jbilander/A500_Edge_Expansion_adapter/KiCad/A500_86pin_internal_adapter.sch

## KiCad design KiCad/A500_86pin_internal_adapter.sch (2021-07-18)

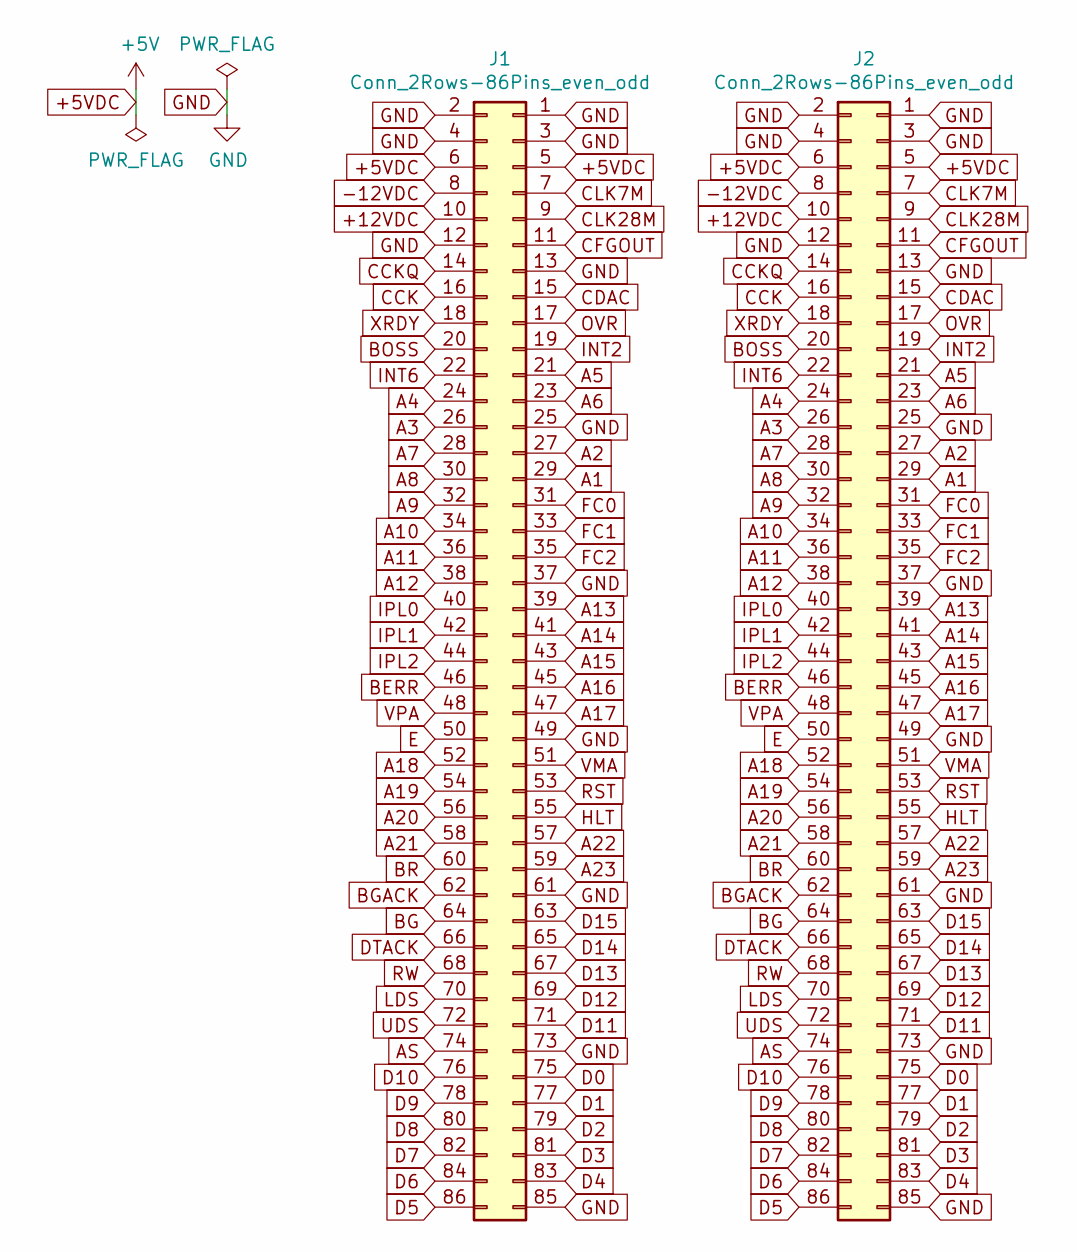
[picture p12: schematic A500_86pin_internal_adapter.sch]

Parts:
J1, J2: Conn_2Rows-86Pins_even_odd; DIP-86_even_odd_W5.08mm

Connections:
+5V: J1.5, J1.6, J2.5, J2.6
+12VDC: J1.10, J2.10
-12VDC: J1.8, J2.8
A1: J1.29, J2.29
A2: J1.27, J2.27
A3: J1.26, J2.26
A4: J1.24, J2.24
A5: J1.21, J2.21
A6: J1.23, J2.23
A7: J1.28, J2.28
A8: J1.30, J2.30
A9: J1.32, J2.32
A10: J1.34, J2.34
A11: J1.36, J2.36
A12: J1.38, J2.38
A13: J1.39, J2.39
A14: J1.41, J2.41
A15: J1.43, J2.43
A16: J1.45, J2.45
A17: J1.47, J2.47
A18: J1.52, J2.52
A19: J1.54, J2.54
A20: J1.56, J2.56
A21: J1.58, J2.58
A22: J1.57, J2.57
A23: J1.59, J2.59
AS: J1.74, J2.74
BERR: J1.46, J2.46
BG: J1.64, J2.64
BGACK: J1.62, J2.62
BOSS: J1.20, J2.20
BR: J1.60, J2.60
CCK: J1.16, J2.16
CCKQ: J1.14, J2.14
CDAC: J1.15, J2.15
CFGOUT: J1.11, J2.11
CLK7M: J1.7, J2.7
CLK28M: J1.9, J2.9
D0: J1.75, J2.75
D1: J1.77, J2.77
D2: J1.79, J2.79
D3: J1.81, J2.81
D4: J1.83, J2.83
D5: J1.86, J2.86
D6: J1.84, J2.84
D7: J1.82, J2.82
D8: J1.80, J2.80
D9: J1.78, J2.78
D10: J1.76, J2.76
D11: J1.71, J2.71
D12: J1.69, J2.69
D13: J1.67, J2.67
D14: J1.65, J2.65
D15: J1.63, J2.63
DTACK: J1.66, J2.66
E: J1.50, J2.50
FC0: J1.31, J2.31
FC1: J1.33, J2.33
FC2: J1.35, J2.35
GND: J1.1, J1.2, J1.3, J1.4, J1.12, J1.13, J1.25, J1.37, J1.49, J1.61, J1.73, J1.85, J2.1, J2.2, J2.3, J2.4, J2.12, J2.13, J2.25, J2.37, J2.49, J2.61, J2.73, J2.85
HLT: J1.55, J2.55
INT2: J1.19, J2.19
INT6: J1.22, J2.22
IPL0: J1.40, J2.40
IPL1: J1.42, J2.42
IPL2: J1.44, J2.44
LDS: J1.70, J2.70
OVR: J1.17, J2.17
RST: J1.53, J2.53
RW: J1.68, J2.68
UDS: J1.72, J2.72
VMA: J1.51, J2.51
VPA: J1.48, J2.48
XRDY: J1.18, J2.18
